Board-Folk/PregnantLaserMouse/Pregnant Laser Mouse.kicad_sch

## KiCad design Pregnant Laser Mouse.kicad_sch (2024-10-20)

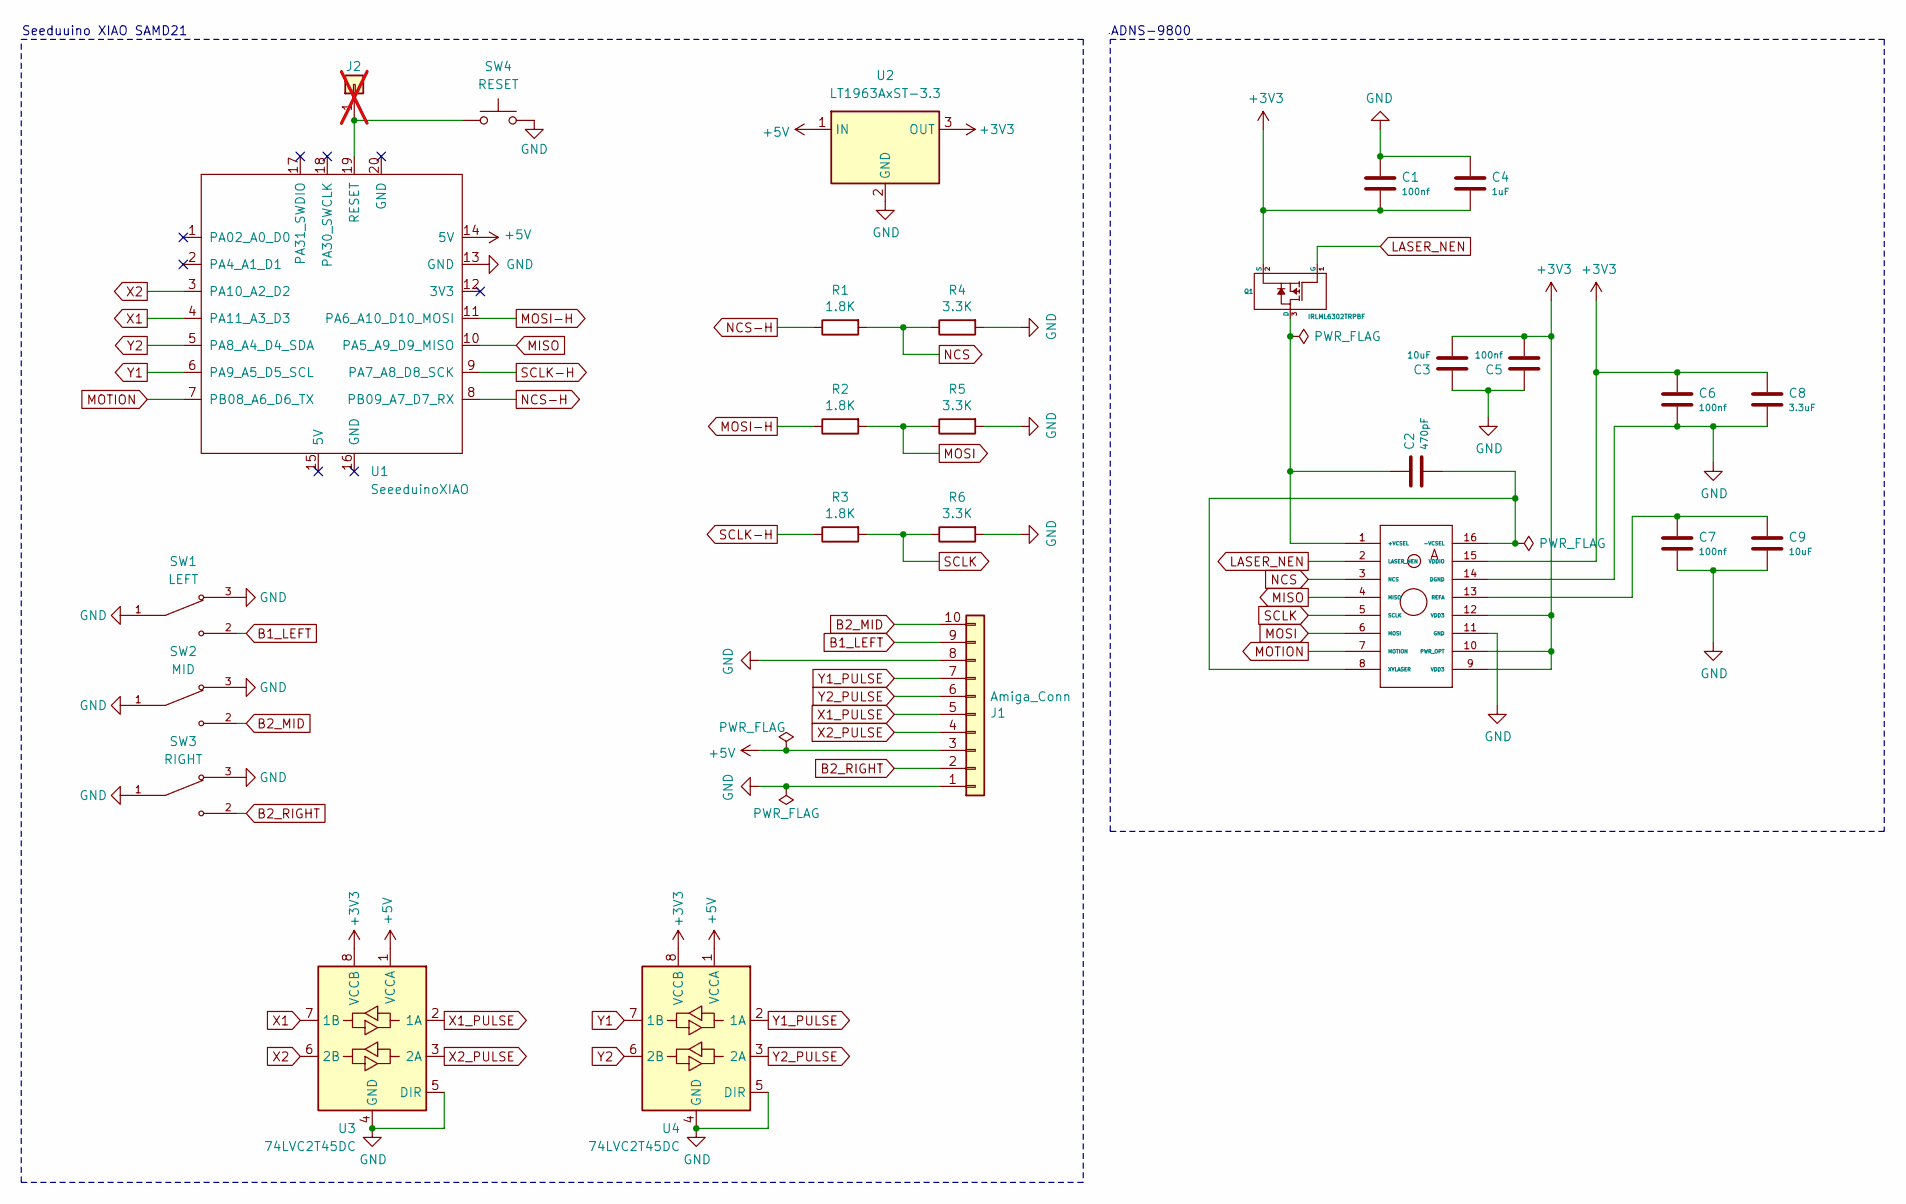
[picture p12: schematic Pregnant Laser Mouse.kicad_sch]

Parts:
C1, C5, C6, C7: 100nf; C_0805_2012Metric; Digikey 399-C0805C104K5RAC7210CT-ND
C2: 470pF; C_0805_2012Metric; Digikey 399-C0805C471K5RAC7800CT-ND
C3, C9: 10uF; C_0805_2012Metric; Digikey 399-C0805C106K8PAC7800CT-ND
C4: 1uF; C_0805_2012Metric; Digikey 399-C0805C105K4RAC7800CT-ND
C8: 3.3uF; C_0805_2012Metric; Digikey 399-C0805C335K8PAC7800CT-ND
J1: Amiga_Conn; PinHeader_1x10_P2.54mm_Vertical; Digikey 2057-PH1-10-UA-ND
J2: Reset Hole; ResetHole; not fitted
M1: ADNS-9800; Digikey Aliexpress Get Lens Also
Q1: IRLML6302TRPBF; SOT-23; Digikey IRLML6302PBFCT-ND / DMG2301LK-7DICT-ND
R1, R2, R3: 1.8K; R_0805_2012Metric; Digikey 2019-RK73H2ATTD1801FCT-ND
R4, R5, R6: 3.3K; R_0805_2012Metric; Digikey 2019-RK73H2ATTD3301FCT-ND
SW1: LEFT; SW_D2F-01F; Digikey SW501-ND
SW2: MID; SW_D2F-01F; Digikey SW501-ND
SW3: RIGHT; SW_D2F-01F; Digikey SW501-ND
SW4: RESET; SW_PUSH_6mm_H4.3mm; Digikey 450-1650-ND
U1: SeeeduinoXIAO; Seeeduino XIAO-MOUDLE14P-2.54-21X17.8MM; Digikey 1597-102010328-ND
U2: LT1963AxST-3.3; SOT-223-3_TabPin2; Digikey AP7361C-33E-13DICT-ND
U3, U4: 74LVC2T45DC; VSSOP-8_2.3x2mm_P0.5mm; Digikey 1727-4578-1-ND

Connections:
+3V3: C1.2, C3.2, C4.2, C5.2, C6.1, C8.1, M1.9 (VDD3), M1.10 (PWR_OPT), M1.12 (VDD3), M1.15 (VDDIO), Q1.2 (S), U2.3 (OUT), U3.8 (VCCB), U4.8 (VCCB)
+5V: J1.3, U1.14 (5V), U2.1 (IN), U3.1 (VCCA), U4.1 (VCCA)
B1_LEFT: J1.9, SW1.2
B2_MID: J1.10, SW2.2
B2_RIGHT: J1.2, SW3.2
GND: C1.1, C3.1, C4.1, C5.1, C6.2, C7.2, C8.2, C9.2, J1.1, J1.8, M1.11 (GND), M1.14 (DGND), R4.2, R5.2, R6.2, SW1.1, SW1.3, SW2.1, SW2.3, SW3.1, SW3.3, SW4.2, U1.13 (GND), U2.2 (GND), U3.4 (GND), U3.5 (DIR), U4.4 (GND), U4.5 (DIR)
LASER_NEN: M1.2 (LASER_NEN), Q1.1 (G)
MISO: M1.4 (MISO), U1.10 (PA5_A9_D9_MISO)
MOSI: M1.6 (MOSI), R2.2, R5.1
MOSI-H: R2.1, U1.11 (PA6_A10_D10_MOSI)
MOTION: M1.7 (MOTION), U1.7 (PB08_A6_D6_TX)
NCS: M1.3 (NCS), R1.2, R4.1
NCS-H: R1.1, U1.8 (PB09_A7_D7_RX)
unnamed: C2.1, M1.1 (+VCSEL), Q1.3 (D)
unnamed: C2.2, M1.8 (XYLASER), M1.16 (-VCSEL)
unnamed: C7.1, C9.1, M1.13 (REFA)
unnamed: J2.1, SW4.1, U1.19 (RESET)
SCLK: M1.5 (SCLK), R3.2, R6.1
SCLK-H: R3.1, U1.9 (PA7_A8_D8_SCK)
X1: U1.4 (PA11_A3_D3), U3.7 (1B)
X1_PULSE: J1.5, U3.2 (1A)
X2: U1.3 (PA10_A2_D2), U3.6 (2B)
X2_PULSE: J1.4, U3.3 (2A)
Y1: U1.6 (PA9_A5_D5_SCL), U4.7 (1B)
Y1_PULSE: J1.7, U4.2 (1A)
Y2: U1.5 (PA8_A4_D4_SDA), U4.6 (2B)
Y2_PULSE: J1.6, U4.3 (2A)

Notes on the sheet:
ADNS-9800
Seeduuino XIAO SAMD21
